mylez/cpu/kicad-projects/old-ram-slice/ram-slice/ram-slice.kicad_pcb

## KiCad design kicad-projects/old-ram-slice/ram-slice/ram-slice.kicad_pcb (2020-08-02, an earlier design)

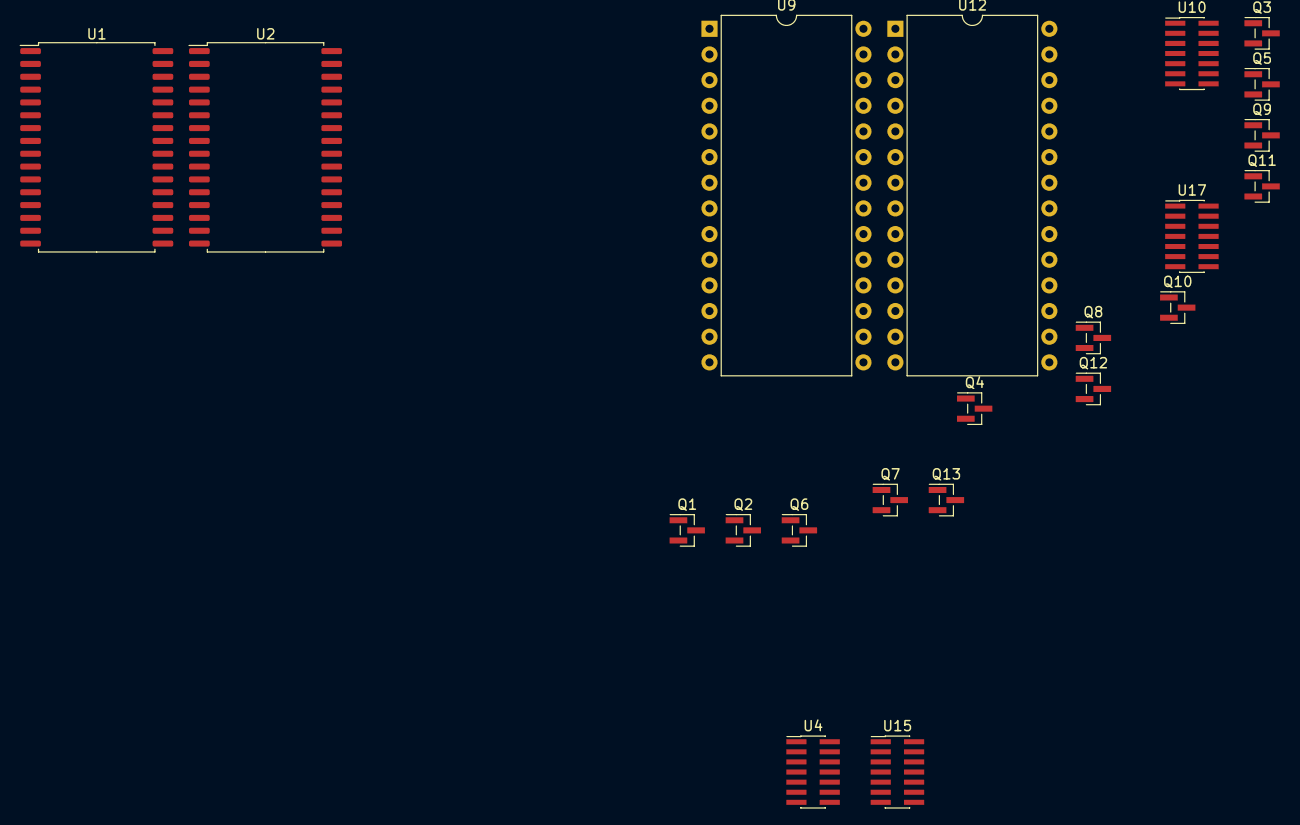
[picture p8: board ram-slice.kicad_pcb from above]

Board: 2 copper layers, 21 parts (0 on the bottom side), 42 nets, no tracks yet.

Parts:
Q1, Q2, Q3, Q4, Q5, Q6, Q7, Q8, Q9, Q10, Q11, Q12, Q13: BS170; PinHeader_1x03_P1.00mm_Vertical_SMD_Pin1Left
U1, U2: IS61C5128AS-25QLI; SSOP-32_11.305x20.495mm_P1.27mm
U4, U10: 74LS08; PinHeader_2x07_P1.00mm_Vertical_SMD
U9, U12: 27C64; DIP-28_W15.24mm
U15: 74LS02; PinHeader_2x07_P1.00mm_Vertical_SMD
U17: 74LS32; PinHeader_2x07_P1.00mm_Vertical_SMD

Connections:
/A1: U1.12, U2.12, U9.10, U12.10
/A2: U1.11, U2.11, U9.9, U12.9
/A3: U1.10, U2.10, U9.8, U12.8
/A4: U1.9, U2.9, U9.7, U12.7
/A5: U1.8, U2.8, U9.6, U12.6
/A6: U1.7, U2.7, U9.5, U12.5
/A7: U1.6, U2.6, U9.4, U12.4
/A8: U1.5, U2.5, U9.3, U12.3
/A9: U1.27, U2.27, U9.25, U12.25
/A10: U1.26, U2.26, U9.24, U12.24
/A11: U1.23, U2.23, U9.21, U12.21
/A12: U1.25, U2.25, U9.23, U12.23
/A13: U1.4, U2.4, U9.2, U12.2
/A14: U1.28, U2.28
/A15: U1.3, U2.3
/A16: U1.31, U2.31
/A17: U1.2, U2.2
/A18: U1.1, U2.1
/A19: U1.30, U2.30
/BYTE: U4.2, U10.2
/HIGH0: U2.13, U12.11
/HIGH1: U2.14, U12.12
/HIGH2: U2.15, U12.13
/HIGH3: U2.17, U12.15
/HIGH4: U2.18, U12.16
/HIGH5: U2.19, U12.17
/HIGH6: U2.20, U12.18
/HIGH7: U2.21, U12.19
/HIGH_BYTE: U4.3, U17.4
/LOW0: U1.13, U9.11
/LOW1: U1.14, U9.12
/LOW2: U1.15, U9.13
/LOW3: U1.17, U9.15
/LOW4: U1.18, U9.16
/LOW5: U1.19, U9.17
/LOW6: U1.20, U9.18
/LOW7: U1.21, U9.19
/LOW_BYTE: U10.3, U17.1
/LOW_BYTE_ACCESSED: U17.3, U17.6
/STORE: U10.4, U10.9
/~BYTE: U17.2, U17.5
/~CLK: U10.5, U10.10
