mylez/cpu/kicad-projects/register-slice/register-slice.kicad_pcb

## KiCad design kicad-projects/register-slice/register-slice.kicad_pcb (2020-08-02)

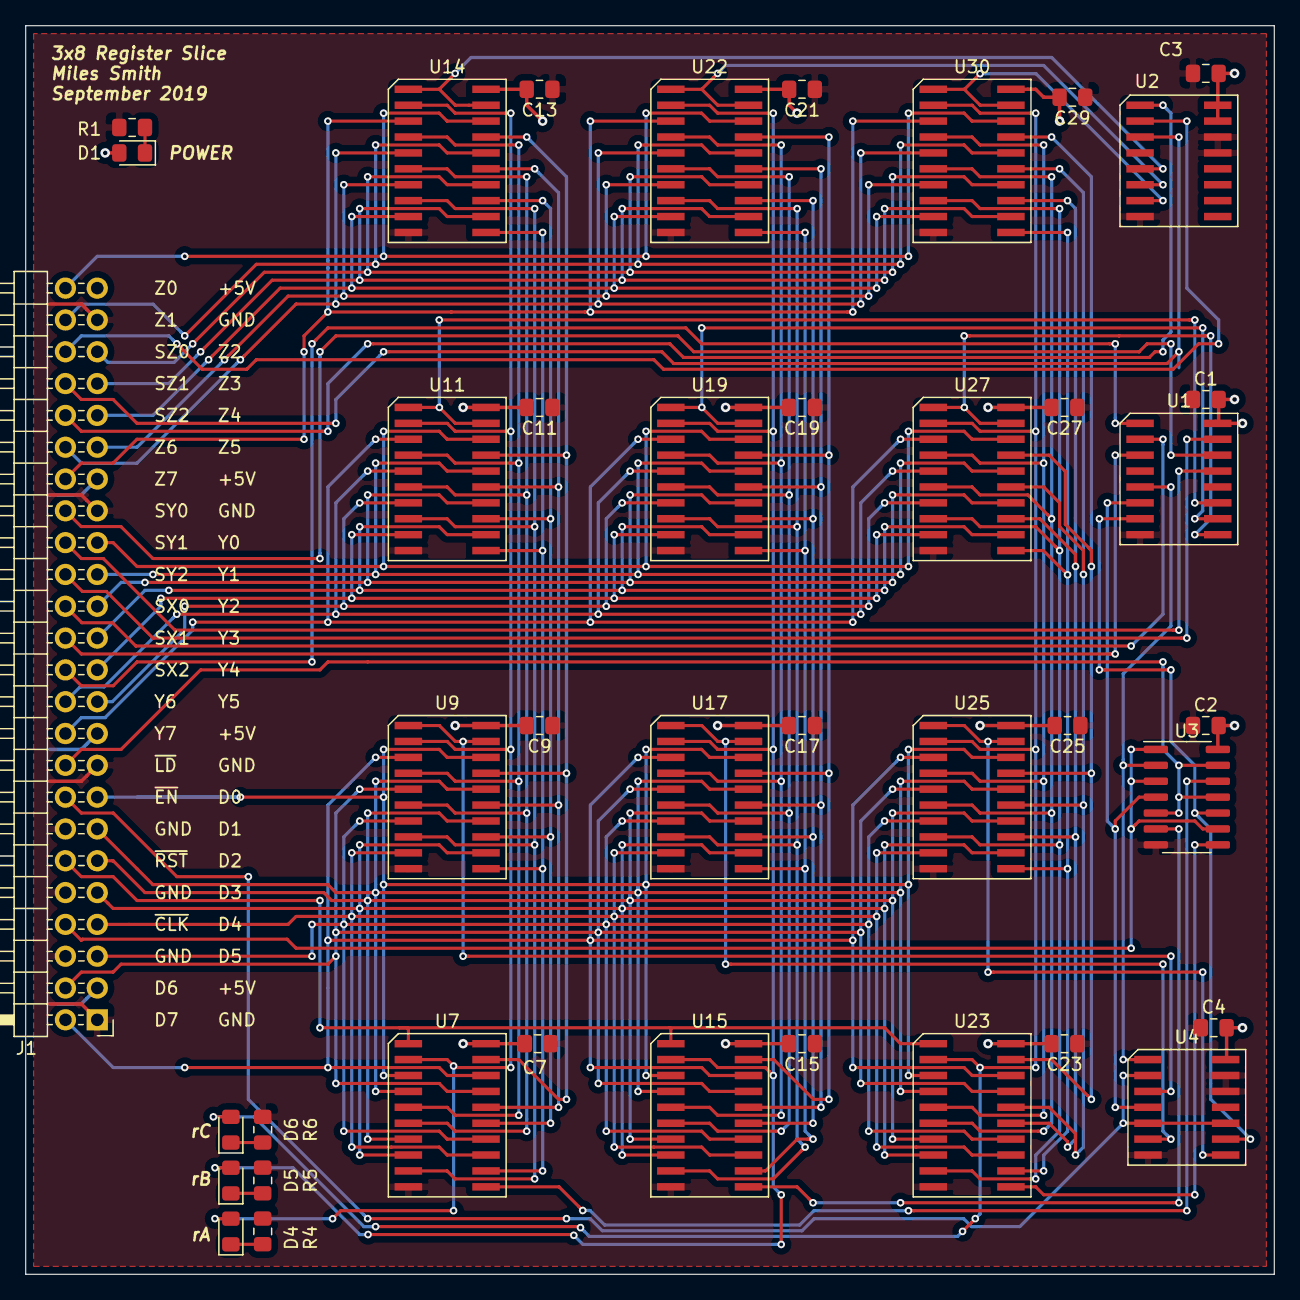
[picture p9: board register-slice.kicad_pcb from above]

Board: 2 copper layers, 99.7 x 99.7 mm, 41 parts (0 on the bottom side), 82 nets.

Parts:
C1, C2, C3, C4, C7, C9, C11, C13, C15, C17, C19, C21, C23, C25, C27, C29: 0.1 uF; C_0805_2012Metric_Pad1.15x1.40mm_HandSolder
D1: GREEN; LED_0805_2012Metric_Pad1.15x1.40mm_HandSolder
D4, D5, D6: RED; LED_0805_2012Metric_Pad1.15x1.40mm_HandSolder
J1: Conn_02x24_Odd_Even; PinHeader_2x24_P2.54mm_Horizontal
R1, R4, R5, R6: 430; R_0805_2012Metric_Pad1.15x1.40mm_HandSolder
U1, U2: 74LS139; SOIC-16-6.2mm
U3: 74LS27; SOIC-14_3.9x8.7mm_P1.27mm
U4: 74LS32; SOIC-14-6.2mm
U7, U15, U23: 74LS273; SOIC-20-6.2mm
U9, U11, U14, U17, U19, U22, U25, U27, U30: 74LS244; SOIC-20-6.2mm

Connections:
+5V: C1.2, C2.2, C3.2, C4.2, C7.2, C9.2, C11.2, C13.2, C15.2, C17.2, C19.2, C21.2, C23.2, C25.2, C27.2, C29.2, D1.2, J1.3, J1.19, J1.35, J1.47, U1.16, U2.15, U2.16, U3.14, U4.14, U7.20, U9.20, U11.20, U14.20, U15.20, U17.20, U19.20, U22.20, U23.20, U25.20, U27.20, U30.20
/R0A: D4.2, U7.2, U9.2, U11.2, U14.2
/R0B: D5.2, U15.2, U17.2, U19.2, U22.2
/R0C: D6.2, U23.2, U25.2, U27.2, U30.2
/register_a/CP: U3.12, U7.11
/register_a/R1: U7.5, U9.4, U11.4, U14.4
/register_a/R2: U7.6, U9.6, U11.6, U14.6
/register_a/R3: U7.9, U9.8, U11.8, U14.8
/register_a/R4: U7.12, U9.11, U11.11, U14.11
/register_a/R5: U7.15, U9.13, U11.13, U14.13
/register_a/R6: U7.16, U9.15, U11.15, U14.15
/register_a/R7: U7.19, U9.17, U11.17, U14.17
/register_a/~EN_X: U4.3, U9.1, U9.19
/register_b/CP: U3.6, U15.11
/register_b/R1: U15.5, U17.4, U19.4, U22.4
/register_b/R2: U15.6, U17.6, U19.6, U22.6
/register_b/R3: U15.9, U17.8, U19.8, U22.8
/register_b/R4: U15.12, U17.11, U19.11, U22.11
/register_b/R5: U15.15, U17.13, U19.13, U22.13
/register_b/R6: U15.16, U17.15, U19.15, U22.15
/register_b/R7: U15.19, U17.17, U19.17, U22.17
/register_b/~EN_X: U4.6, U17.1, U17.19
/register_c/CP: U3.8, U23.11
/register_c/R1: U23.5, U25.4, U27.4, U30.4
/register_c/R2: U23.6, U25.6, U27.6, U30.6
/register_c/R3: U23.9, U25.8, U27.8, U30.8
/register_c/R4: U23.12, U25.11, U27.11, U30.11
/register_c/R5: U23.15, U25.13, U27.13, U30.13
/register_c/R6: U23.16, U25.15, U27.15, U30.15
/register_c/R7: U23.19, U25.17, U27.17, U30.17
/register_c/~EN_X: U4.8, U25.1, U25.19
/~EN_1_X: U1.5, U3.2, U4.1
/~EN_1_Y: U1.11, U11.1, U11.19
/~EN_1_Z: U2.5, U14.1, U14.19
/~EN_2_X: U1.6, U3.4, U4.4
/~EN_2_Y: U1.10, U19.1, U19.19
/~EN_2_Z: U2.6, U22.1, U22.19
/~EN_3_X: U1.7, U3.10, U4.9
/~EN_3_Y: U1.9, U27.1, U27.19
/~EN_3_Z: U2.7, U30.1, U30.19
D0: J1.15, U7.3, U9.18, U15.3, U17.18, U23.3, U25.18
D1: J1.13, U7.4, U9.16, U15.4, U17.16, U23.4, U25.16
D2: J1.11, U7.7, U9.14, U15.7, U17.14, U23.7, U25.14
D3: J1.9, U7.8, U9.12, U15.8, U17.12, U23.8, U25.12
D4: J1.7, U7.13, U9.9, U15.13, U17.9, U23.13, U25.9
D5: J1.5, U7.14, U9.7, U15.14, U17.7, U23.14, U25.7
D6: J1.4, U7.17, U9.5, U15.17, U17.5, U23.17, U25.5
D7: J1.2, U7.18, U9.3, U15.18, U17.3, U23.18, U25.3
GND: C1.1, C2.1, C3.1, C4.1, C7.1, C9.1, C11.1, C13.1, C15.1, C17.1, C19.1, C21.1, C23.1, C25.1, C27.1, C29.1, J1.1, J1.6, J1.10, J1.14, J1.17, J1.33, J1.45, R1.2, R4.2, R5.2, R6.2, U1.8, U2.8, U2.13, U2.14, U3.7, U4.7, U4.12, U4.13, U7.10, U9.10, U11.10, U14.10, U15.10, U17.10, U19.10, U22.10, U23.10, U25.10, U27.10, U30.10
unnamed: D1.1, R1.1
unnamed: D4.1, R4.1
unnamed: D5.1, R5.1
unnamed: D6.1, R6.1
SEL_X_0: J1.28, U1.2
SEL_X_1: J1.26, U1.3
SEL_Y_0: J1.34, U1.14
SEL_Y_1: J1.32, U1.13
SEL_Z_0: J1.44, U2.2
SEL_Z_1: J1.42, U2.3
Y0: J1.31, U11.18, U19.18, U27.18
Y1: J1.29, U11.16, U19.16, U27.16
Y2: J1.27, U11.14, U19.14, U27.14
Y3: J1.25, U11.12, U19.12, U27.12
Y4: J1.23, U11.9, U19.9, U27.9
Y5: J1.21, U11.7, U19.7, U27.7
Y6: J1.22, U11.5, U19.5, U27.5
Y7: J1.20, U11.3, U19.3, U27.3
Z0: J1.48, U14.18, U22.18, U30.18
Z1: J1.46, U14.16, U22.16, U30.16
Z2: J1.43, U14.14, U22.14, U30.14
Z3: J1.41, U14.12, U22.12, U30.12
Z4: J1.39, U14.9, U22.9, U30.9
Z5: J1.37, U14.7, U22.7, U30.7
Z6: J1.38, U14.5, U22.5, U30.5
Z7: J1.36, U14.3, U22.3, U30.3
~CLK: J1.8, U3.1, U3.3, U3.9
~EN_REG_D: J1.16, U4.2, U4.5, U4.10
~REG_LOAD: J1.18, U3.5, U3.11, U3.13
~RESET: J1.12, U7.1, U15.1, U23.1
~SEL_X_2: J1.24, U1.1
~SEL_Y_2: J1.30, U1.15
~SEL_Z_2: J1.40, U2.1
